sparkfun/SparkFun_Qwiic_Pocket_Dev_Board_ESP32_C6/docs/assets/images/Qwiic_Pocket_Dev-USB.jpg

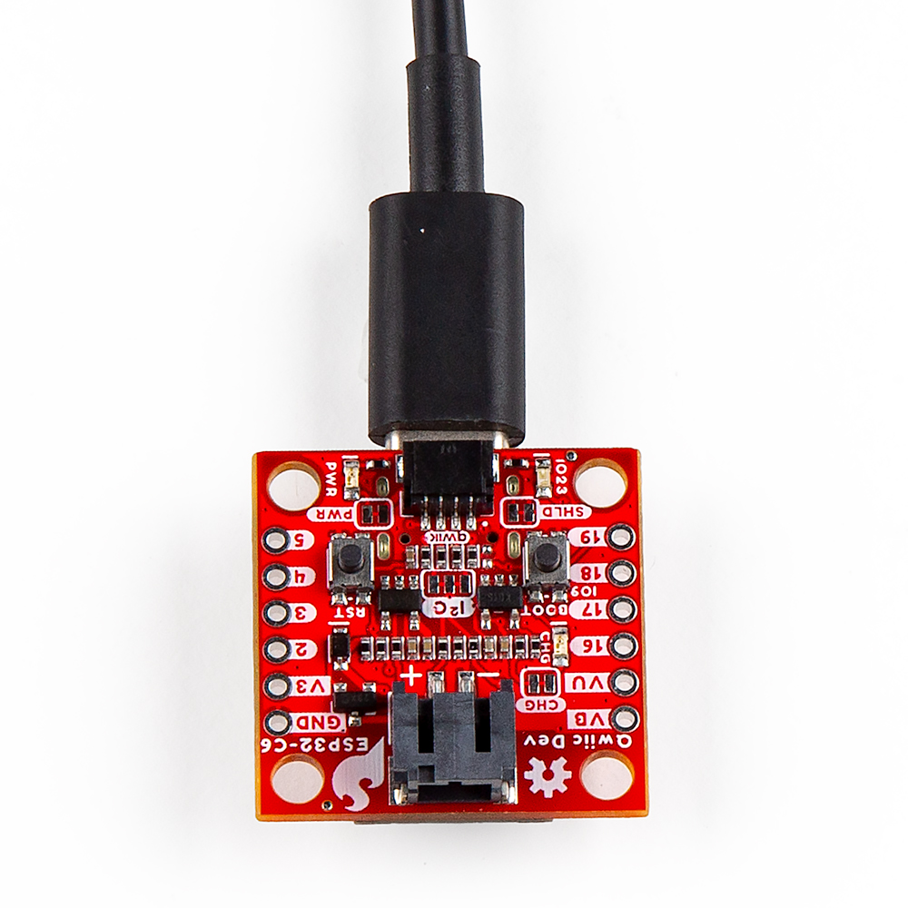
docs/assets/images/Qwiic_Pocket_Dev-USB.jpg
